jithinsisaac/WLR089U0-SAMR34-Dev-Board-LoRaWAN/Pics/IMG_20210307_152220.jpg

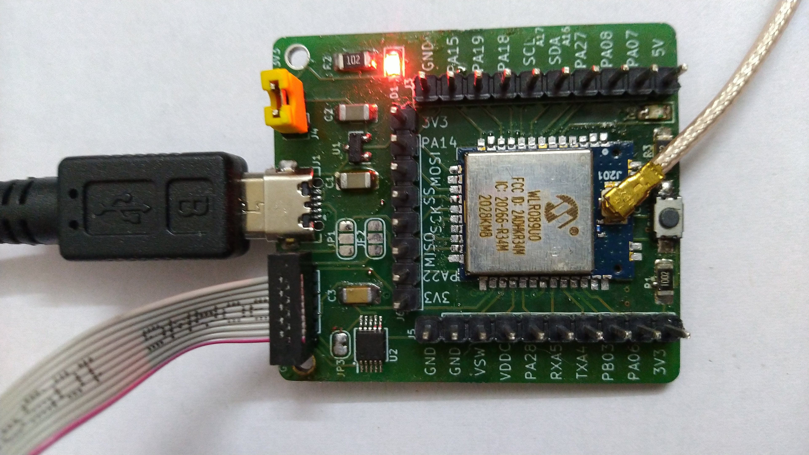
Pics/IMG_20210307_152220.jpg
